Cortesse/humidificadorPortatil/hardware/kicad/placa/placa.kicad_pcb

## KiCad design hardware/SuperVNA/analog.kicad_sch

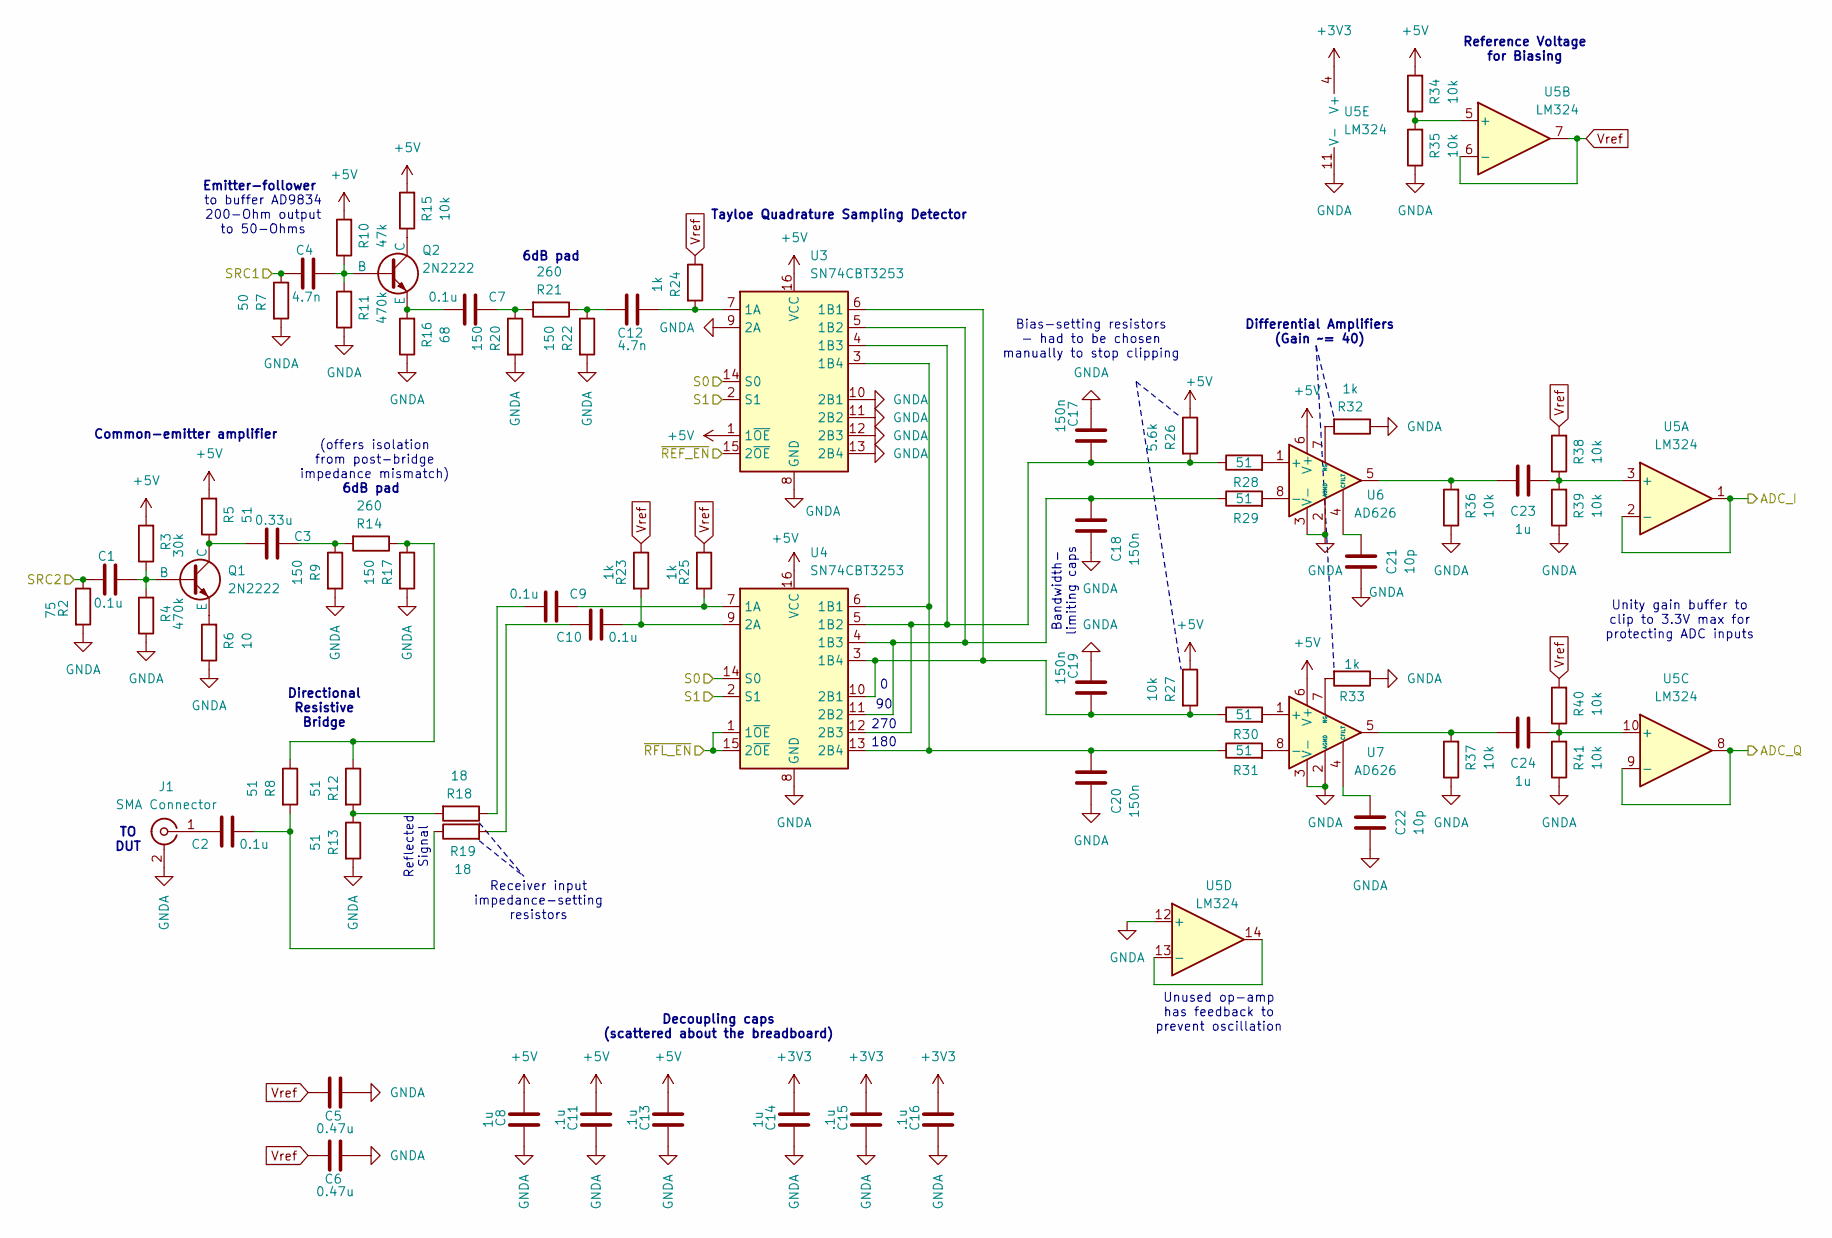
[picture p3: schematic analog.kicad_sch]

Parts:
C1, C2, C7, C9, C10: 0.1u
C3: 0.33u
C4, C12: 4.7n
C5, C6: 0.47u
C8, C14, C23, C24: 1u
C11, C13, C15, C16: .1u
C17, C18, C19, C20: 150n
C21, C22: 10p
J1: SMA Connector
Q1, Q2: 2N2222
R2: 75
R3: 30k
R4, R11: 470k
R5, R8, R12, R13, R28, R29, R30, R31: 51
R6: 10
R7: 50
R9, R17, R20, R22: 150
R10: 47k
R14, R21: 260
R15, R27, R34, R35, R36, R37, R38, R39, R40, R41: 10k
R16: 68
R18, R19: 18
R23, R24, R25, R32, R33: 1k
R26: 5.6k
U3, U4: SN74CBT3253
U5: LM324
U6, U7: AD626

Connections:
+3V3: C14.2, C15.2, C16.2, U5.4 (V+)
+5V: C8.2, C11.2, C13.2, R3.2, R5.2, R10.2, R15.2, R26.1, R27.1, R34.2, U3.1 (1~OE), U3.16 (VCC), U4.16 (VCC), U6.6 (V+), U7.6 (V+)
ADC_I: U5.1, U5.2 (-)
ADC_Q: U5.8, U5.9 (-)
GNDA: C5.1, C6.1, C8.1, C11.1, C13.1, C14.1, C15.1, C16.1, C17.2, C18.2, C19.2, C20.2, C21.2, C22.2, J1.2 (Ext), R2.2, R4.1, R6.1, R7.2, R9.2, R11.1, R13.2, R16.1, R17.2, R20.2, R22.2, R32.1, R33.1, R35.1, R36.1, R37.1, R39.1, R41.1, U3.8 (GND), U3.9 (2A), U3.10 (2B1), U3.11 (2B2), U3.12 (2B3), U3.13 (2B4), U4.8 (GND), U5.11 (V-), U5.12 (+), U6.2 (AGND), U6.3 (V-), U7.2 (AGND), U7.3 (V-)
unnamed: C1.2, Q1.2 (B), R3.1, R4.2
unnamed: C2.1, R8.2, R19.1
unnamed: C2.2, J1.1 (In)
unnamed: C3.1, R9.1, R14.2
unnamed: C3.2, Q1.1 (C), R5.1
unnamed: C4.2, Q2.2 (B), R10.1, R11.2
unnamed: C7.1, Q2.3 (E), R16.2
unnamed: C7.2, R20.1, R21.2
unnamed: C9.1, R18.1
unnamed: C9.2, R25.2, U4.7 (1A)
unnamed: C10.1, R23.2, U4.9 (2A)
unnamed: C10.2, R19.2
unnamed: C12.1, R24.2, U3.7 (1A)
unnamed: C12.2, R21.1, R22.1
unnamed: C17.1, R26.2, R28.1, U3.4 (1B3), U4.5 (1B2), U4.12 (2B3)
unnamed: C18.1, R29.1, U3.5 (1B2), U4.4 (1B3), U4.11 (2B2)
unnamed: C19.1, R27.2, R30.1, U3.6 (1B1), U4.3 (1B4), U4.10 (2B1)
unnamed: C20.1, R31.1, U3.3 (1B4), U4.6 (1B1), U4.13 (2B4)
unnamed: C21.1, U6.4 (CFILT)
unnamed: C22.1, U7.4 (CFILT)
unnamed: C23.1, R38.1, R39.2, U5.3 (+)
unnamed: C23.2, R36.2, U6.5
unnamed: C24.1, R40.1, R41.2, U5.10 (+)
unnamed: C24.2, R37.2, U7.5
unnamed: Q1.3 (E), R6.2
unnamed: Q2.1 (C), R15.1
unnamed: R8.1, R12.1, R14.1, R17.1
unnamed: R12.2, R13.1, R18.2
unnamed: R28.2, U6.1 (+)
unnamed: R29.2, U6.8 (-)
unnamed: R30.2, U7.1 (+)
unnamed: R31.2, U7.8 (-)
unnamed: R32.2, U6.7 (RG)
unnamed: R33.2, U7.7 (RG)
unnamed: R34.1, R35.2, U5.5 (+)
unnamed: U5.13 (-), U5.14
S0: U3.14 (S0), U4.14 (S0)
S1: U3.2 (S1), U4.2 (S1)
SRC1: C4.1, R7.1
SRC2: C1.1, R2.1
Vref: C5.2, C6.2, R23.1, R24.1, R25.1, R38.2, R40.2, U5.6 (-), U5.7
~REF_EN: U3.15 (2~OE)
~RFL_EN: U4.1 (1~OE), U4.15 (2~OE)

Notes on the sheet:
Decoupling caps (scattered about the breadboard)
Unused op-amp has feedback to prevent oscillation
to buffer AD9834 200-Ohm output to 50-Ohms
Bandwidth- limiting caps
(offers isolation from post-bridge impedance mismatch)
Bias-setting resistors - had to be chosen manually to stop clipping
270
6dB pad
Unity gain buffer to clip to 3.3V max for protecting ADC inputs
TO DUT
180
Reflected Signal
Reference Voltage for Biasing
Common-emitter amplifier
Emitter-follower
Receiver input impedance-setting resistors
Tayloe Quadrature Sampling Detector
Differential Amplifiers (Gain ~= 40)
Directional Resistive Bridge
